HTangl/IMPS/Pictures/IMG20231104193543.jpg

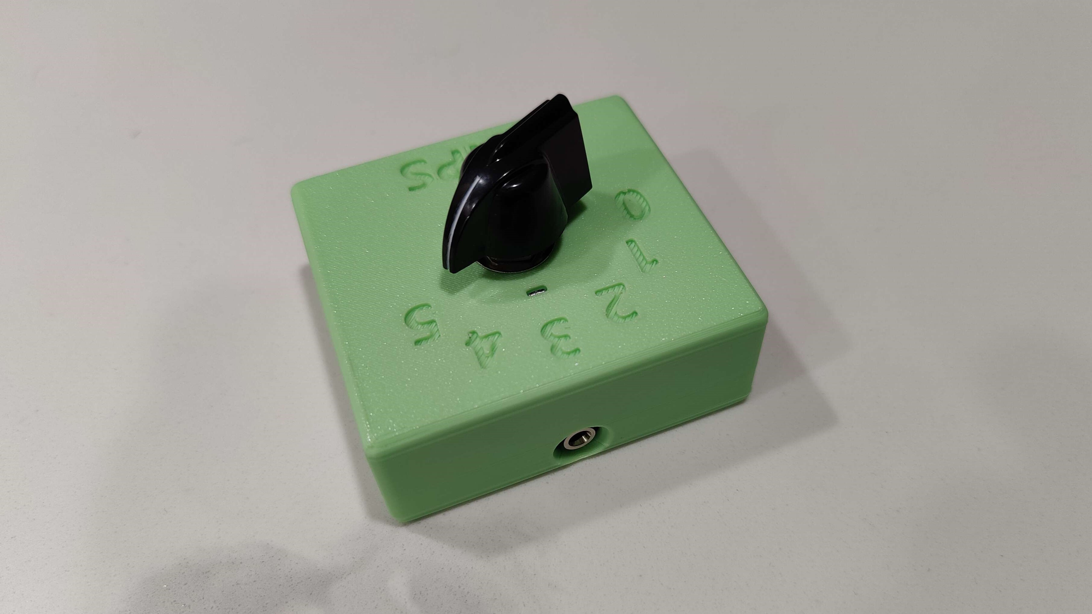
Pictures/IMG20231104193543.jpg
