HTangl/IMPS/Pictures/IMG20231106221302.jpg

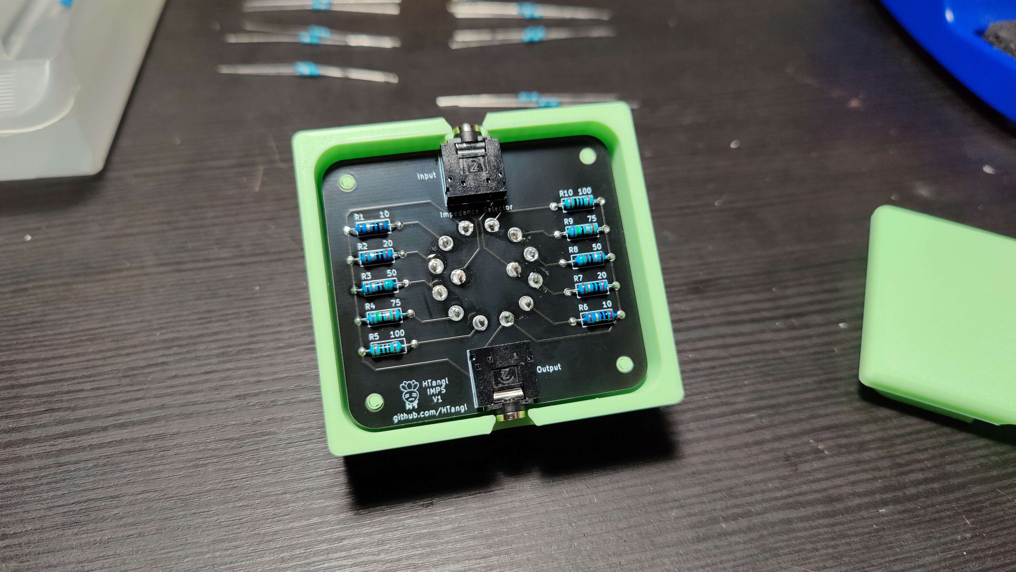
Pictures/IMG20231106221302.jpg
