HTangl/IMPS/Pictures/IMG20231114204134_1.jpg

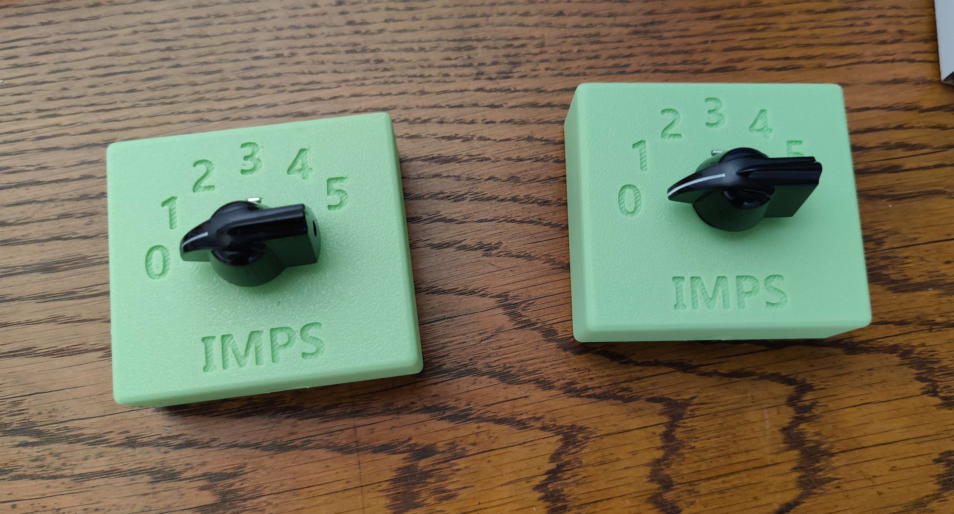
Pictures/IMG20231114204134_1.jpg
